glassblowing/molds/mold-designs/insert-mold/foot_plate_solid.dxf

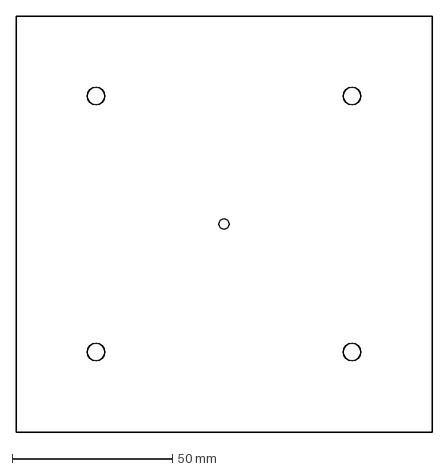
[picture p21: CAD file, 2026-10-08]
mold-designs/insert-mold/foot_plate_solid.dxf
130.0 x 130.0 mm
