glassblowing/molds/mold-designs/insert-mold/inserts/pineapple.step

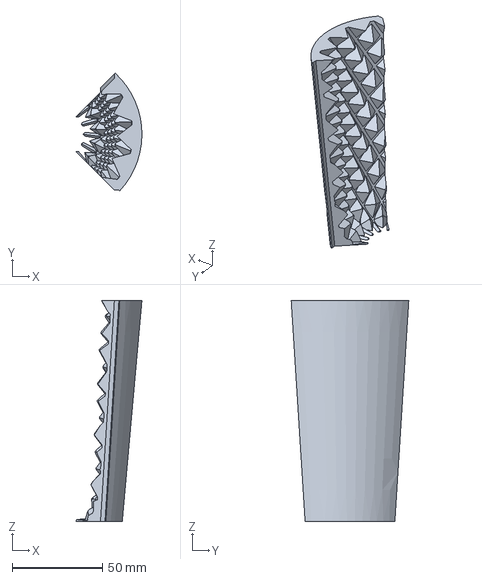
[picture p22: CAD file, 2026-10-08]
mold-designs/insert-mold/inserts/pineapple.step
36.4 x 65.0 x 122.2 mm
