glassblowing/molds/mold-designs/optic/sunburst.step

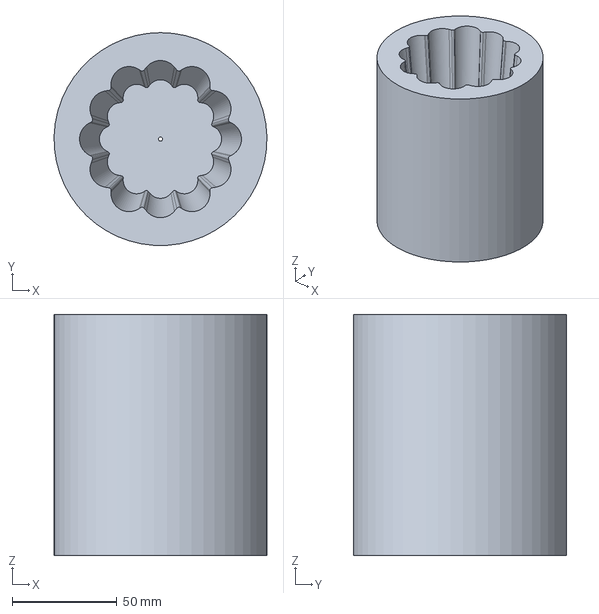
[picture p23: CAD file, 2026-10-08]
mold-designs/optic/sunburst.step
101.6 x 101.5 x 115.0 mm
