glassblowing/molds/mold-designs/segmented/base_plate.dxf

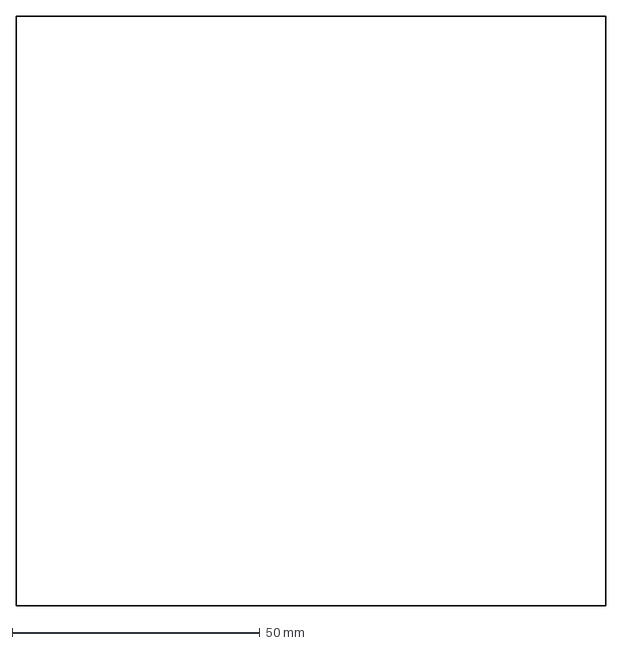
[picture p25: CAD file, 2026-10-08]
mold-designs/segmented/base_plate.dxf
118.9 x 118.9 mm
