glassblowing/molds/mold-designs/insert-mold/inserts/spiral.step

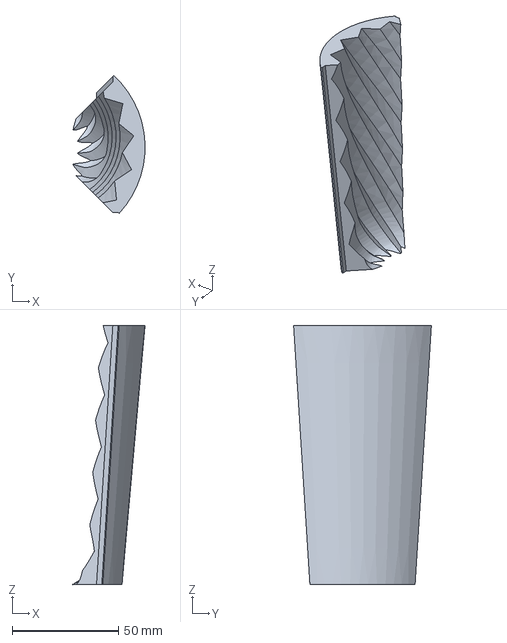
[picture p26: CAD file, 2026-10-08]
mold-designs/insert-mold/inserts/spiral.step
34.0 x 65.0 x 122.2 mm
