glassblowing/molds/mold-designs/pineapple/plates/plate_12.dxf

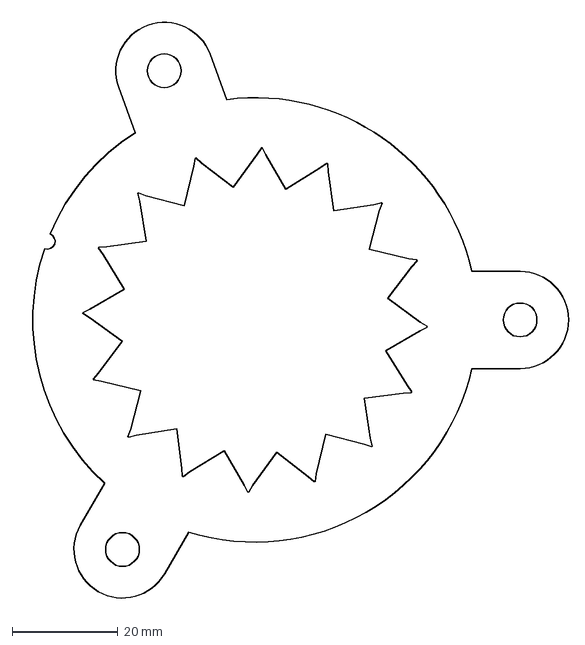
[picture p27: CAD file, 2026-10-08]
mold-designs/pineapple/plates/plate_12.dxf
104.6 x 111.5 mm
