glassblowing/molds/mold-designs/segmented/glass.step

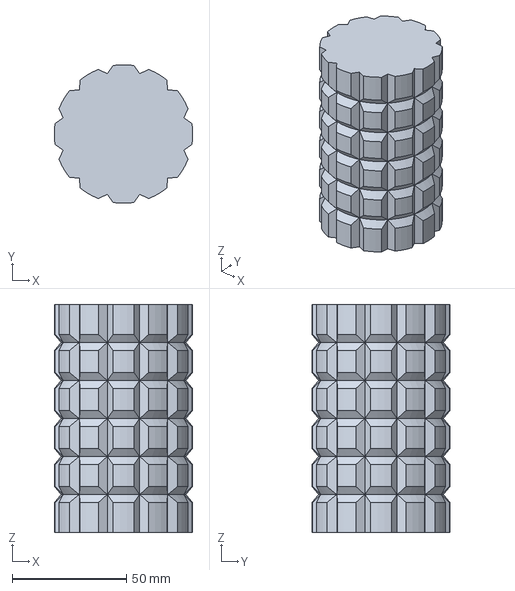
[picture p28: CAD file, 2026-10-08]
mold-designs/segmented/glass.step
60.7 x 60.7 x 100.0 mm
