glassblowing/molds/mold-designs/insert-mold/sleeve_solid.step

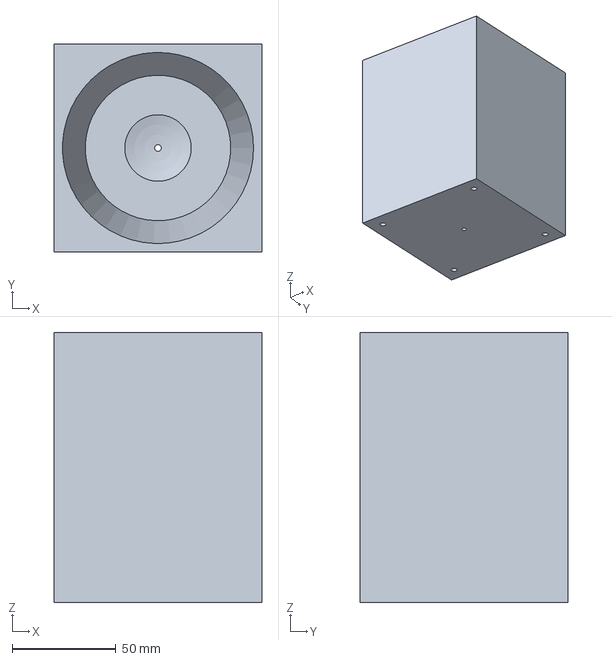
[picture p29: CAD file, 2026-10-08]
mold-designs/insert-mold/sleeve_solid.step
100.0 x 100.0 x 130.0 mm
