glassblowing/molds/mold-designs/pineapple/plates/plate_34.dxf

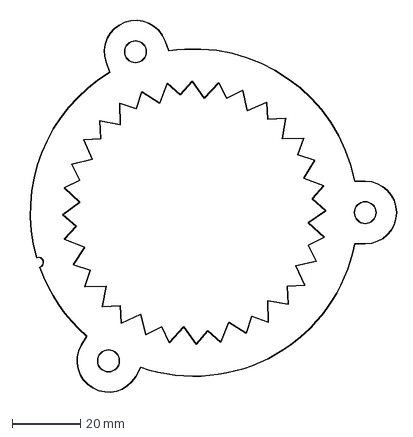
[picture p30: CAD file, 2026-10-08]
mold-designs/pineapple/plates/plate_34.dxf
111.5 x 111.5 mm
