glassblowing/molds/mold-designs/pineapple/plates/plate_06.dxf

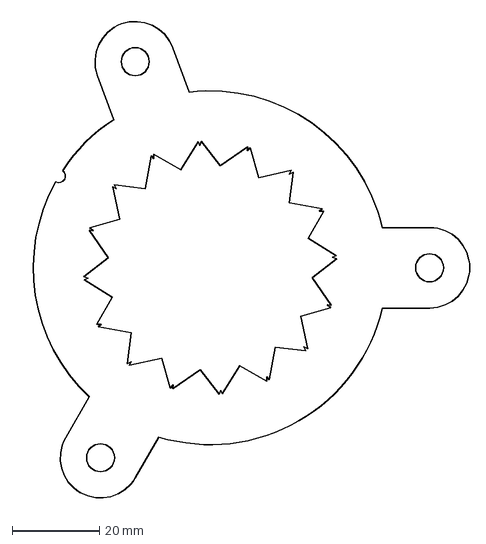
[picture p31: CAD file, 2026-10-08]
mold-designs/pineapple/plates/plate_06.dxf
103.8 x 111.5 mm
