glassblowing/molds/mold-designs/pineapple/plates/plate_41.dxf

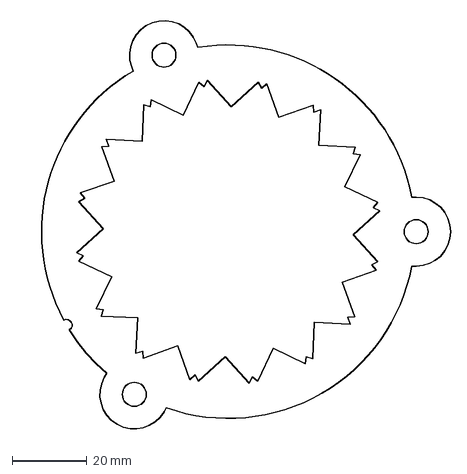
[picture p33: CAD file, 2026-10-08]
mold-designs/pineapple/plates/plate_41.dxf
116.0 x 111.5 mm
