glassblowing/molds/mold-designs/pineapple/plates/plate_40.dxf

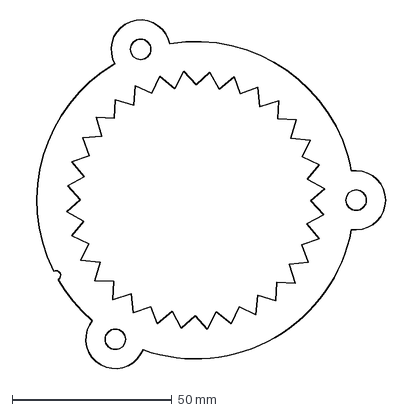
[picture p34: CAD file, 2026-10-08]
mold-designs/pineapple/plates/plate_40.dxf
115.4 x 111.5 mm
