glassblowing/molds/mold-designs/pineapple/plates/plate_24.dxf

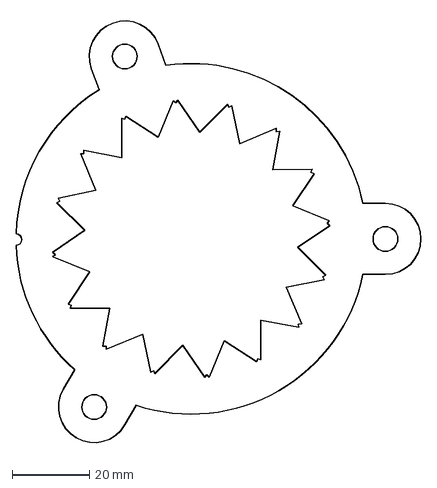
[picture p35: CAD file, 2026-10-08]
mold-designs/pineapple/plates/plate_24.dxf
104.7 x 111.5 mm
