glassblowing/molds/mold-designs/pineapple/plates/plate_39.dxf

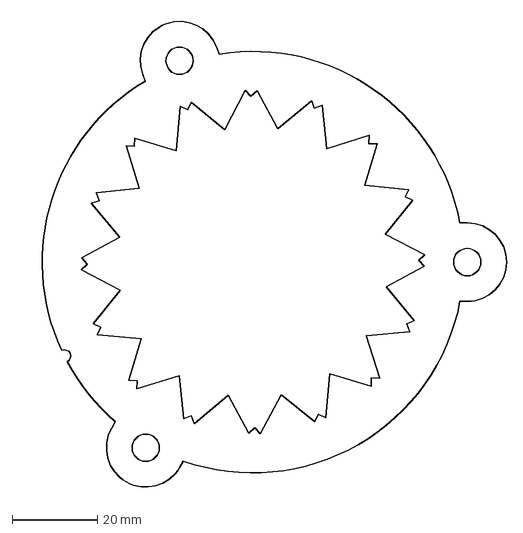
[picture p36: CAD file, 2026-10-08]
mold-designs/pineapple/plates/plate_39.dxf
114.8 x 111.5 mm
