glassblowing/molds/mold-designs/pineapple/plates/plate_07.dxf

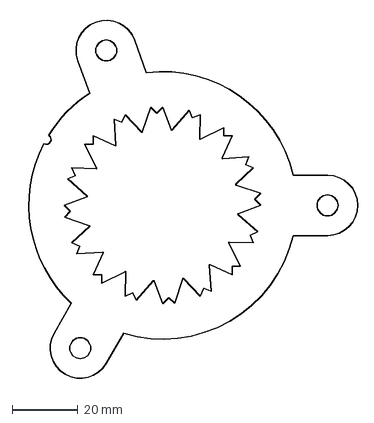
[picture p37: CAD file, 2026-10-08]
mold-designs/pineapple/plates/plate_07.dxf
104.0 x 111.5 mm
