glassblowing/molds/mold-designs/pineapple/plates/plate_35.dxf

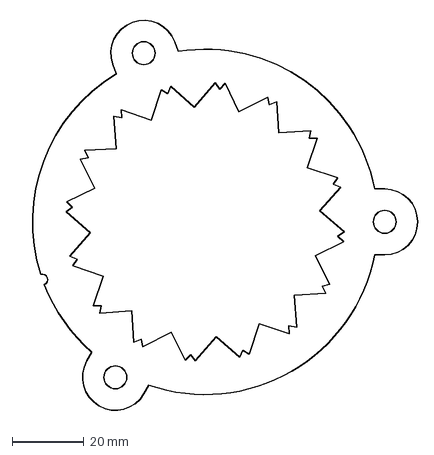
[picture p39: CAD file, 2026-10-08]
mold-designs/pineapple/plates/plate_35.dxf
112.2 x 111.5 mm
