glassblowing/molds/mold-designs/pineapple/plates/plate_36.dxf

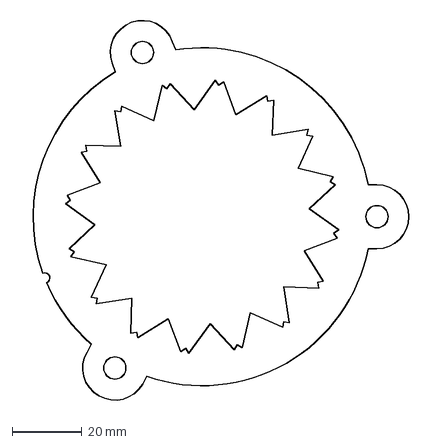
[picture p41: CAD file, 2026-10-08]
mold-designs/pineapple/plates/plate_36.dxf
112.9 x 111.5 mm
