glassblowing/molds/mold-designs/pineapple/plates/plate_02.dxf

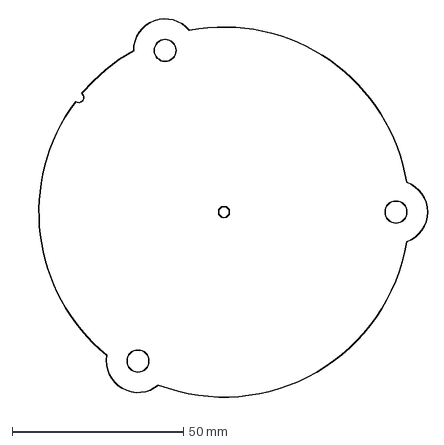
[picture p42: CAD file, 2026-10-08]
mold-designs/pineapple/plates/plate_02.dxf
120.0 x 113.4 mm
