glassblowing/molds/mold-designs/pineapple/plates/plate_31.dxf

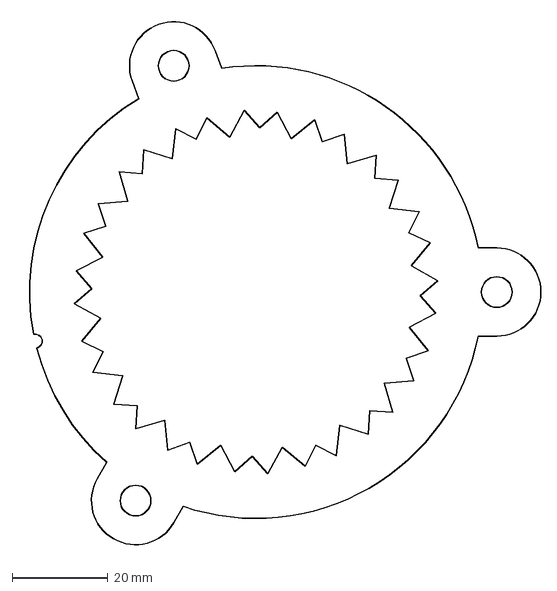
[picture p43: CAD file, 2026-10-08]
mold-designs/pineapple/plates/plate_31.dxf
109.4 x 111.5 mm
