glassblowing/molds/mold-designs/pineapple/plates/plate_33.dxf

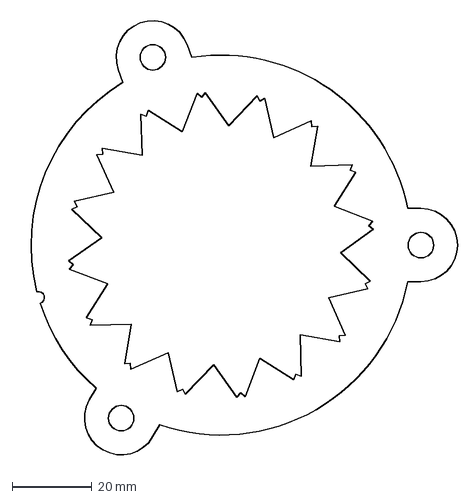
[picture p44: CAD file, 2026-10-08]
mold-designs/pineapple/plates/plate_33.dxf
110.8 x 111.5 mm
