glassblowing/molds/mold-designs/pineapple/plates/plate_29.dxf

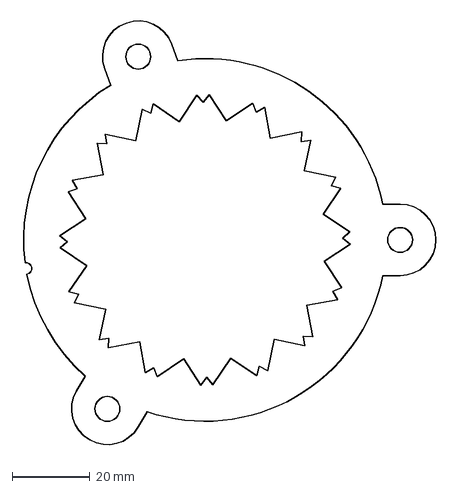
[picture p45: CAD file, 2026-10-08]
mold-designs/pineapple/plates/plate_29.dxf
108.0 x 111.5 mm
