glassblowing/molds/mold-designs/pineapple/plates/plate_15.dxf

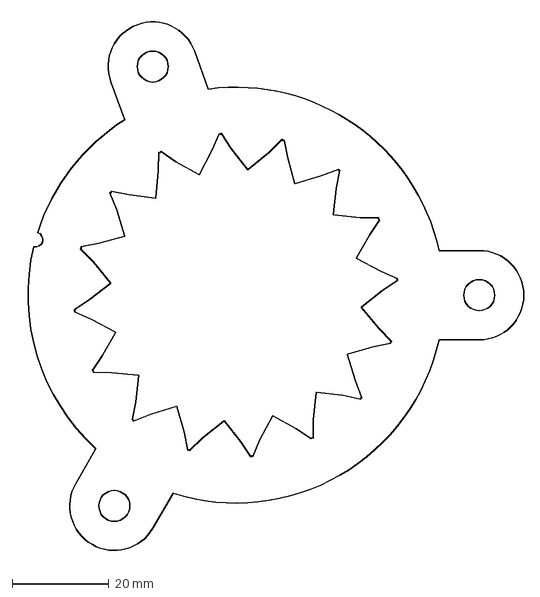
[picture p46: CAD file, 2026-10-08]
mold-designs/pineapple/plates/plate_15.dxf
104.8 x 111.5 mm
