glassblowing/molds/mold-designs/pineapple/plates/plate_26.dxf

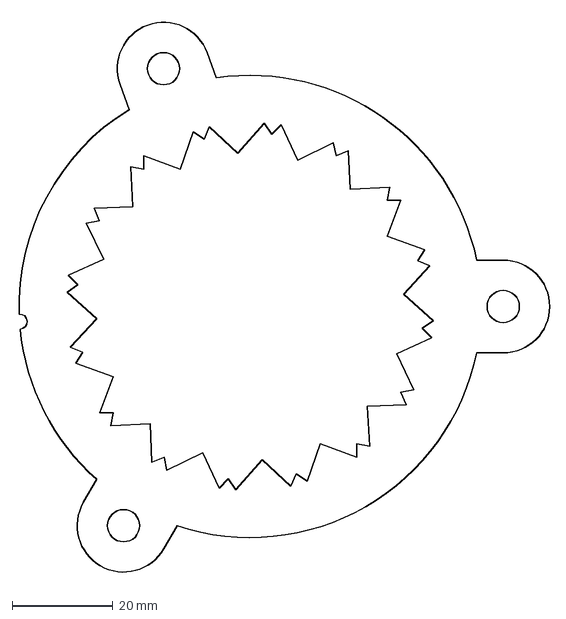
[picture p47: CAD file, 2026-10-08]
mold-designs/pineapple/plates/plate_26.dxf
105.8 x 111.5 mm
