glassblowing/molds/mold-designs/pineapple/plates/plate_28.dxf

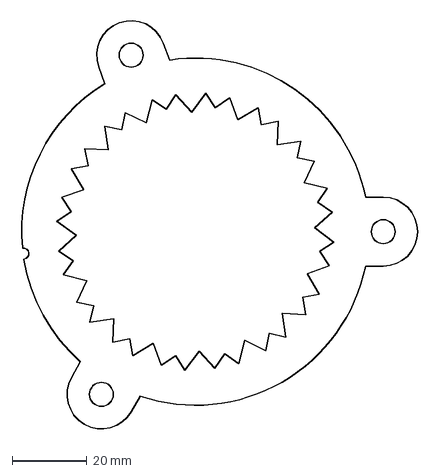
[picture p48: CAD file, 2026-10-08]
mold-designs/pineapple/plates/plate_28.dxf
107.2 x 111.5 mm
