glassblowing/molds/mold-designs/pineapple/plates/plate_38.dxf

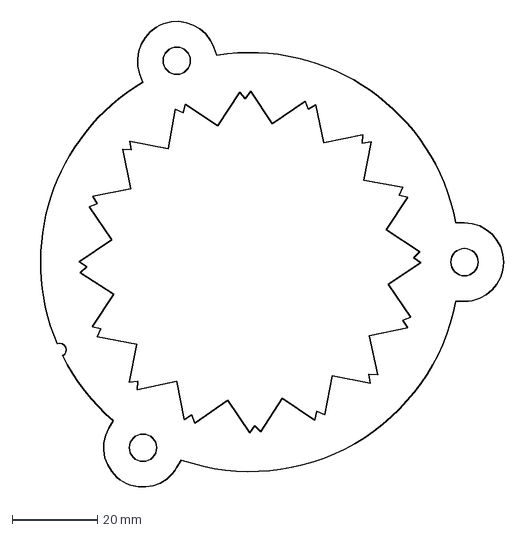
[picture p49: CAD file, 2026-10-08]
mold-designs/pineapple/plates/plate_38.dxf
114.2 x 111.5 mm
