glassblowing/molds/mold-designs/pineapple/plates/plate_23.dxf

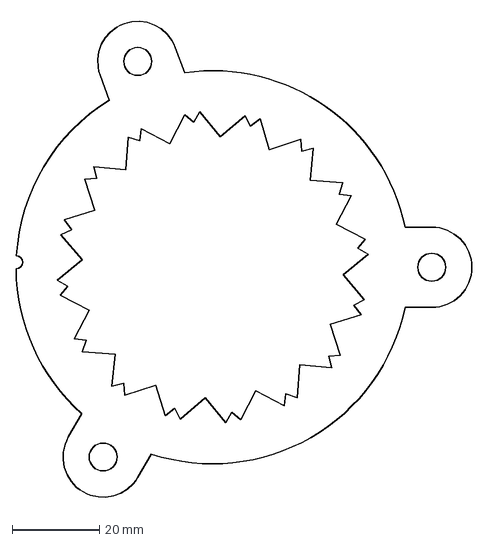
[picture p50: CAD file, 2026-10-08]
mold-designs/pineapple/plates/plate_23.dxf
104.4 x 111.5 mm
