glassblowing/molds/mold-designs/pineapple/plates/plate_10.dxf

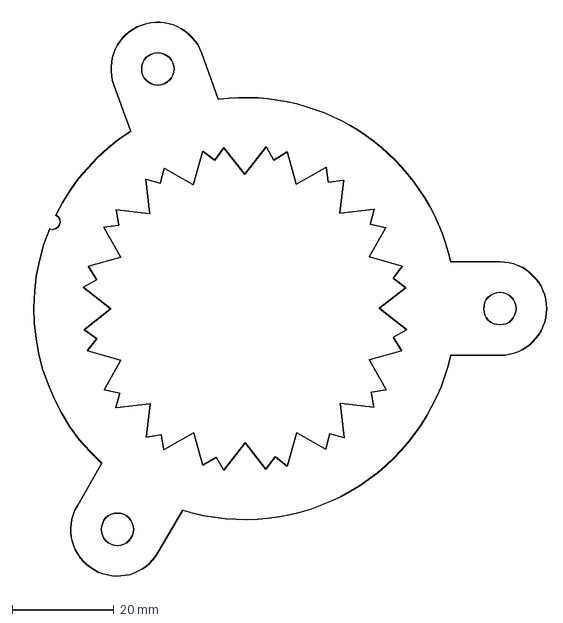
[picture p51: CAD file, 2026-10-08]
mold-designs/pineapple/plates/plate_10.dxf
104.4 x 111.5 mm
