glassblowing/molds/mold-designs/pineapple/plates/plate_08.dxf

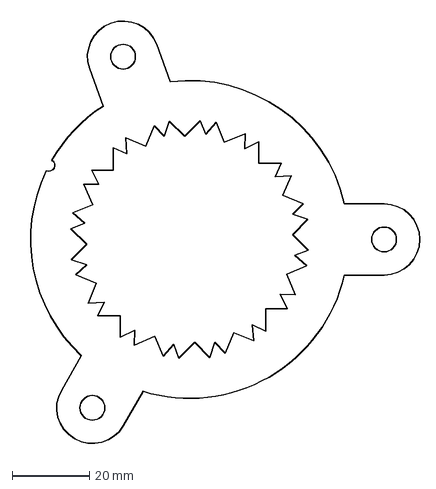
[picture p52: CAD file, 2026-10-08]
mold-designs/pineapple/plates/plate_08.dxf
104.1 x 111.5 mm
