glassblowing/molds/mold-designs/pineapple/plates/plate_37.dxf

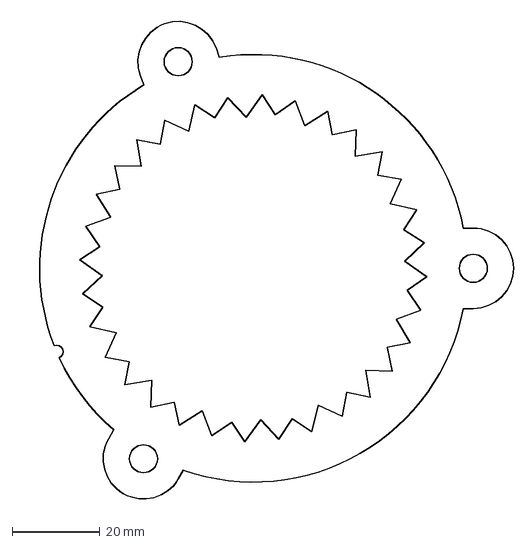
[picture p53: CAD file, 2026-10-08]
mold-designs/pineapple/plates/plate_37.dxf
113.5 x 111.5 mm
