glassblowing/molds/mold-designs/pineapple/plates/plate_01.dxf

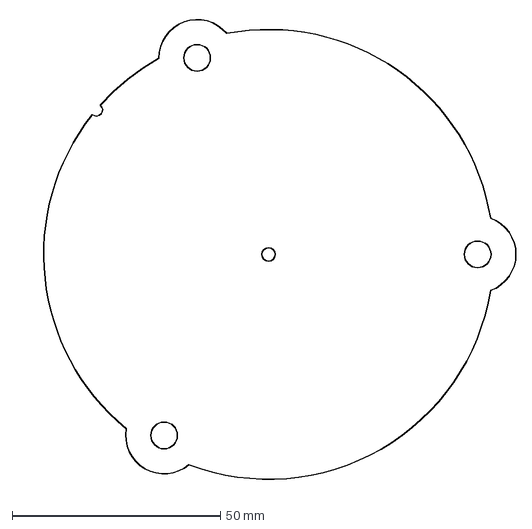
[picture p54: CAD file, 2026-10-08]
mold-designs/pineapple/plates/plate_01.dxf
120.1 x 113.4 mm
