glassblowing/molds/mold-designs/pineapple/plates/plate_05.dxf

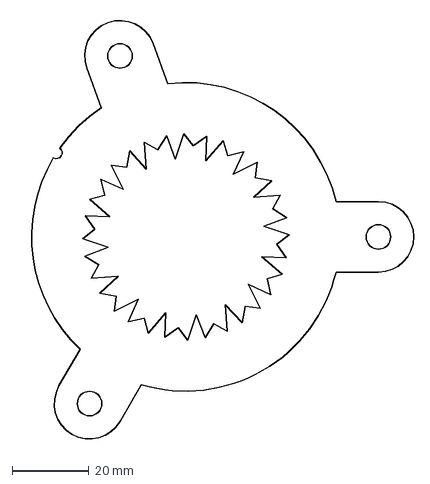
[picture p55: CAD file, 2026-10-08]
mold-designs/pineapple/plates/plate_05.dxf
103.6 x 111.5 mm
