glassblowing/molds/mold-designs/pineapple/plates/plate_19.dxf

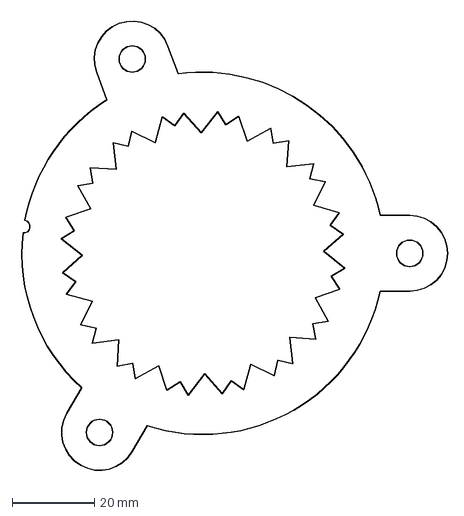
[picture p57: CAD file, 2026-10-08]
mold-designs/pineapple/plates/plate_19.dxf
104.7 x 111.5 mm
