glassblowing/molds/mold-designs/pineapple/plates/plate_22.dxf

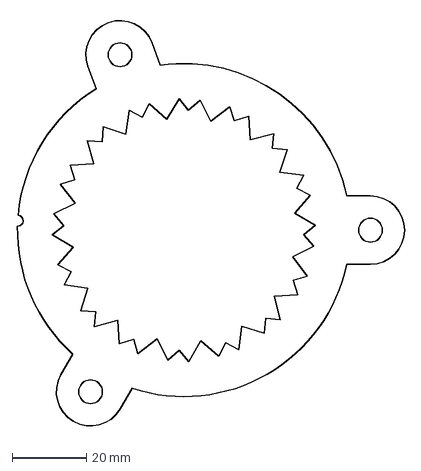
[picture p59: CAD file, 2026-10-08]
mold-designs/pineapple/plates/plate_22.dxf
104.5 x 111.5 mm
