glassblowing/molds/mold-designs/pineapple/plates/plate_04.dxf

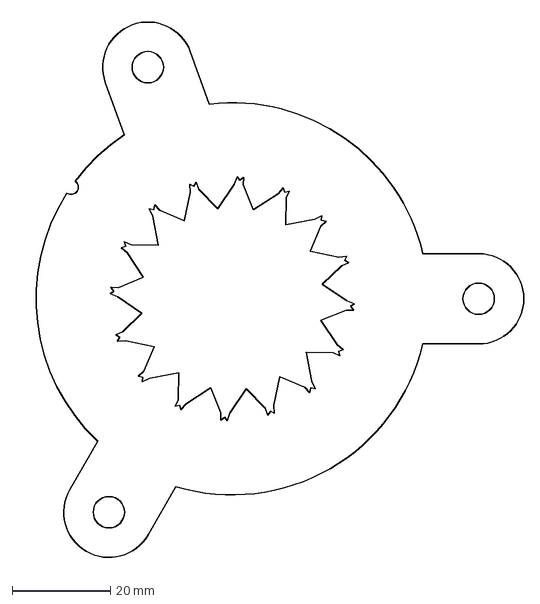
[picture p60: CAD file, 2026-10-08]
mold-designs/pineapple/plates/plate_04.dxf
103.4 x 111.5 mm
