glassblowing/molds/mold-designs/pineapple/plates/plate_09.dxf

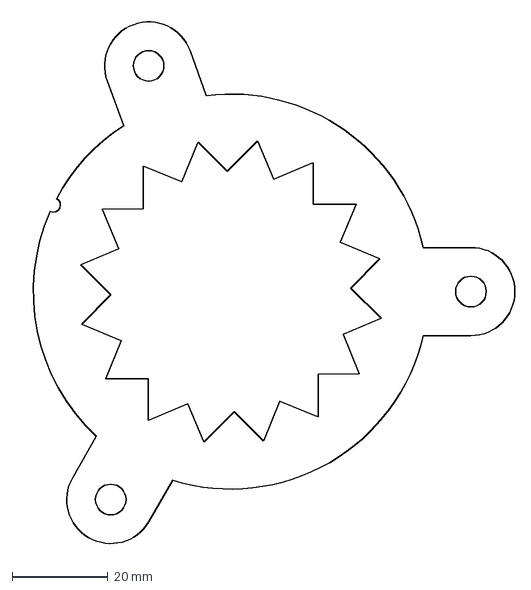
[picture p61: CAD file, 2026-10-08]
mold-designs/pineapple/plates/plate_09.dxf
104.3 x 111.5 mm
