glassblowing/molds/mold-designs/pineapple/plates/plate_14.dxf

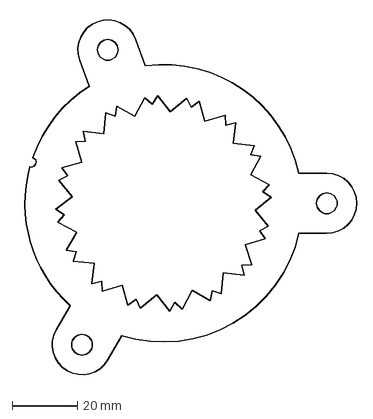
[picture p62: CAD file, 2026-10-08]
mold-designs/pineapple/plates/plate_14.dxf
104.7 x 111.5 mm
