glassblowing/molds/mold-designs/pineapple/plates/plate_25.dxf

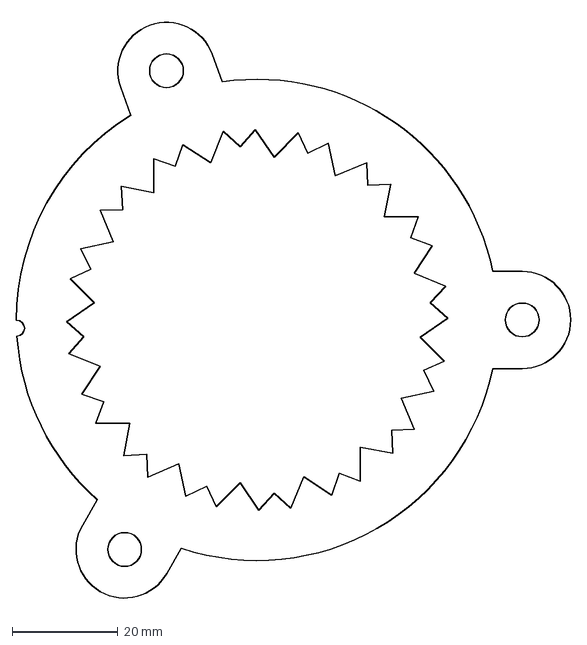
[picture p63: CAD file, 2026-10-08]
mold-designs/pineapple/plates/plate_25.dxf
105.0 x 111.5 mm
