glassblowing/molds/mold-designs/pineapple/plates/plate_11.dxf

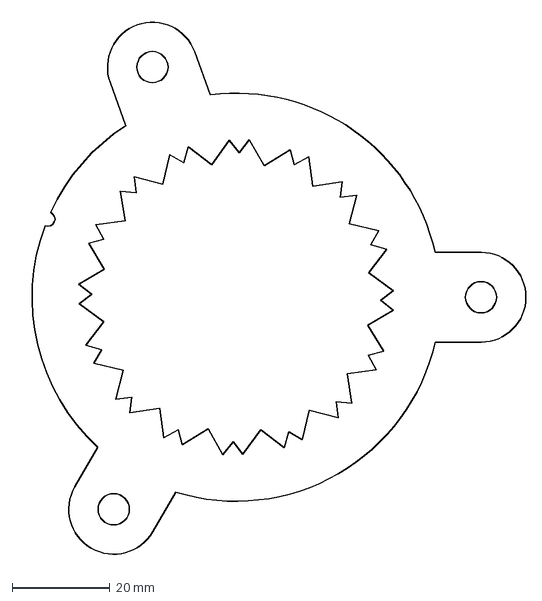
[picture p64: CAD file, 2026-10-08]
mold-designs/pineapple/plates/plate_11.dxf
104.5 x 111.5 mm
