glassblowing/molds/mold-designs/pineapple/plates/plate_30.dxf

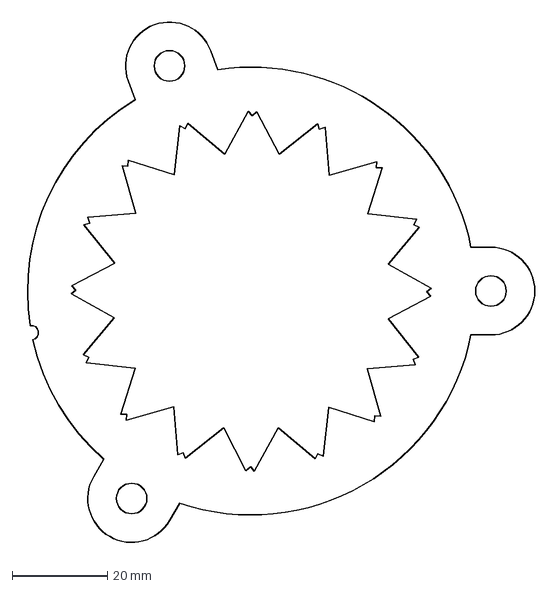
[picture p65: CAD file, 2026-10-08]
mold-designs/pineapple/plates/plate_30.dxf
108.7 x 111.5 mm
