glassblowing/molds/mold-designs/pineapple/plates/plate_03.dxf

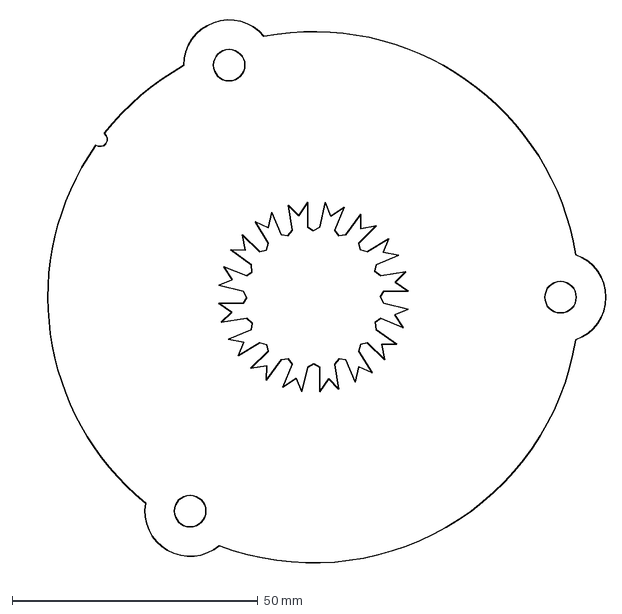
[picture p66: CAD file, 2026-10-08]
mold-designs/pineapple/plates/plate_03.dxf
119.8 x 113.4 mm
